tdaede/internet-of-vinyl/openscad/record_spacers.scad

$fs = 0.01;

difference() {
        cylinder(d=7,h=3);
    cylinder(d=5,h=3);
}
/*
translate([10,0,0]) difference() {
        cylinder(d=7,h=8);
    cylinder(d=5,h=8);
}
/*
